Maitri-13/low-power/Software/Panoptinode/inc/led.h

/*
 * led.h
 *
 *  Created on: Dec 17, 2017
 *      Author: cstewart
 */

#ifndef INC_LED_H_
#define INC_LED_H_


/* set LED */
void led_set(void);

/* clear LED */
void led_clear(void);

/* toggle LED */
void led_toggle(void);

#endif /* INC_LED_H_ */
