Maitri-13/low-power/Software/Panoptinode/inc/spi.h

/*
 * spi.h
 *
 *  Created on: Dec 17, 2017
 *      Author: cstewart
 */

#ifndef INC_SPI_H_
#define INC_SPI_H_

#include "spidrv.h"

extern SPIDRV_HandleData_t SPI_handleData;
extern SPIDRV_Handle_t SPI_handle;


#endif /* INC_SPI_H_ */
